drajnauth/TransistorTracer/Simulations/Testing Stuff/LM358 Amp.asc

R1: res; 10K
R4: res; 6K
R5: res; 1K
U1: opamp2; LM358
uC_Vcontrol: voltage; PULSE(0 4.6 0 4m 4m 0 8m 2)
Vcc: voltage; 14
Named nets: 0, Vout
.tran 20m
.lib TIP120.lib
.lib LM358.sub
.option fastaccess
