drajnauth/TransistorTracer/Simulations/Testing Stuff/PNP & NPN Voltage Amplifier.asc

Q1: npn; 2N3904
Q2: pnp; 2N3906
R1: res; 100K
R2: res; 100R
R3: res; 800K
V1: voltage; 14V
V2: voltage; PULSE(0 2.5 0 4m 4m 0 8m 2)
Named nets: 0, Vout, Vin
.tran 20m
