drajnauth/TransistorTracer/Simulations/Testing Stuff/2N3904 DC Amplifier  (10mA).asc

Q1: npn; 2N3904
Q2: npn; 2N3904
Q3: npn; 2SC5706
R1: res; 1500
R2: res; 10
R3: res; 56K
R4: res; 1500
R5: res; 10
R6: res; 240K
R7: res; 0.1
R8: res; 200
RL: res; 10R
V1: voltage; PULSE(0 4.8 0 5m 5m 0 10m 2)
V2: voltage; 14
Named nets: 0, Vc, Ve, Vb, Vin, Vc2, Ve2, Vb2, Vc3, Ve3, Vb3
.tran 12m
Original - Range of about 3.5V:
R3: 20K
R1, R4: 238R
R2, R5: 2R
R6: 56K
R8: 22 (for 200mA)
 
1st Mod - Wider Range > 4V:
R3: 20K
R1: 200R
R4: 238R
R2: 0R
R5: 1R
R6: 56K
R8: 22 (for 200mA)
 
14V Vcc - Range of about 3.5V:
R3: 20K
R1: 250R
R4: 238R
R2: 0R
R5: 0R
R6: 56K
R8: 22 (for 200mA)
