drajnauth/TransistorTracer/Simulations/Testing Stuff/2N3904 DC Amplifier - Collector Driver (10mA with Neg Feedback).asc

C1: cap; 1n
C2: cap; 14p
C3: cap; 1n
C4: cap; 14p
C5: polcap; 10µ; V=50 Irms=25m Rser=6.7 Lser=0
C6: cap; 10µ
Q1: npn; 2N3904
Q2: npn; 2N3904
Q3: npn; 2SC5706
Q5: npn; 2N3055
R1: res; 1500
R2: res; 10
R3: res; 56K
R4: res; 1500
R5: res; 10
R6: res; 240K
R7: res; 0.1
R8: res; 200
R9: res; 500
R10: res; {R}
R11: res; 462
R12: res; 10
R13: res; 66K
R14: res; 66K
R15: res; 34K
R16: res; 34K
V1: voltage; PULSE(0 4.8 0 5m 5m 0 10m 2)
V2: voltage; 14
V3: voltage; 13
V4: voltage; PULSE(0 4.7 0 1n 1n {DT}  256u); AC 1
V5: voltage; PULSE(0 4.7 128u 1n 1n {DT} 256u); AC 1
Named nets: 0, Vc, Ve, Vb, Vin, Vc2, Ve2, Vb2, Ve3, Vb3, Vadc1, Vadc2, Vpwm
.tran 100m
;.step param R 100 1000 100
.param R 1000
.step param DT 60u 160u 20u
