drajnauth/TransistorTracer/Simulations/Testing Stuff/Arduino PWM Test.asc

C1: polcap; 10µ; V=50 Irms=25m Rser=6.7 Lser=0
C2: polcap; 22µ; V=16 Irms=35m Rser=2.8 Lser=0
C3: polcap; 33µ; V=16 Irms=35m Rser=2.8 Lser=0
R1: res; 56K
R2: res; 200
R3: res; 4
V2: voltage; PULSE(0 4.8 0 1n 1n 128u 256u); AC 1
Named nets: 0, Vout
.tran 0 100m 45m
.step param R 10 200 10
