drajnauth/TransistorTracer/Simulations/Testing Stuff/LM386 Amp.asc

C1: polcap; 47µ; V=16 Irms=186m Rser=0.893291 Lser=4.92432n mfg="Würth Elektronik" pn="860160372007 WCAP-ATLL 5x11" type="Al electrolytic"
C10: polcap; 470µ; V=16 Irms=70m Rser=2.3 Lser=0
C11: polcap; 470µ; V=16 Irms=900m Rser=0.1 Lser=0 mfg="Nichicon" pn="UPH1C471MRH" type="Al electrolytic"
D1: schottky; 1N5817
D2: schottky; 1N5817
R8: res; 250
U1: LM386
V1: voltage; 12
V2: voltage; PULSE(0 2 0 1p 1p 16u 32u); AC 1
Named nets: 0, Vop, Vout
7 BP
1 G1
8 G8
.ac dec 100 1 100Meg
.inc LM386.sub
.tran 0 20m 19m
Convergence is too slow.  Is sufficient current output
Sweep duty cycle.  RMS voltage does not change as expected
