drajnauth/TransistorTracer/Simulations/Testing Stuff/PWM 2N3904 Amplifier.asc

Q1: npn; 2N3904
Q2: npn; 2N3904
R1: res; 1K
R3: res; 120K
R4: res; 100
R6: res; 3R
R7: res; 11K
V1: voltage; PULSE(0 4.8 0 5m 5m 100u 10.1m 2)
V2: voltage; 12
Named nets: 0, Vc, Ve, Vb, Vc2, Ve2, Vb2, Vin
.tran 12m
