drajnauth/TransistorTracer/Simulations/Testing Stuff/Current Ramp.asc

Q1: npn; 2N3904
Q2: npn; 2N3904
Q3: npn; 2N3055
R1: res; 100
R2: res; 10K
R3: res; 10K
R4: res; 10K
V1: voltage; 12
V2: voltage; PULSE(0 4.6 0 500u 500u 10u 1010u 1)
Named nets: 0, Vout
.tran 2m
