drajnauth/TransistorTracer/Simulations/Testing Stuff/Current Switch Test.asc

M1: nmos; 2N7000
R1: res; 100R
R2: res; 15K
R3: res; 500K
V1: voltage; 13.8V
V2: voltage; PULSE(0 5 0 1m 1m 10m 20m 1); AC 1
Named nets: 0
