drajnauth/TransistorTracer/Simulations/Testing Stuff/LM1013 Current Source Test.asc

Q1: npn; 2N2222A
R1: res; 100R
R2: res; 1K
R3: res; 10k
R4: res; 200R
R5: res; 7.14K
U1: LT1013
V1: voltage; 13.8V
V2: voltage; PULSE(0 5 0 5m 5m 15m 30m 1); AC 1
Named nets: 0, Vs
.tran 50m
