drajnauth/TransistorTracer/Simulations/Testing Stuff/LM1013 Peak Detector with Gain Test.asc

C1: polcap; 10µ; V=100 Irms=385m Rser=0.18 Lser=0
C2: polcap; 10µ; V=100 Irms=385m Rser=0.18 Lser=0
C3: polcap; 4.7µ; V=100 Irms=385m Rser=0.18 Lser=0
D1: schottky; 1N5711
D2: schottky; 1N5711
R1: res; 68K
R2: res; 1K
R3: res; 10k
R5: res; 7.14K
U1: LT1013
V1: voltage; 13.8V
V2: voltage; PULSE(0 5 0 1p 1p .5m 1m); AC 1
Named nets: 0, Vout
.tran 0 50m 30m
About 4ms Ripple
Delay 30m get about 16mV variation from 100ms.
