drajnauth/TransistorTracer/Simulations/Testing Stuff/NE5532 Amplifier.asc

C1: cap; 1µ
C2: cap; 1µ
C3: cap; 1µ
R1: res; 10K
R2: res; 1K
R3: res; 47K
R4: res; 47K
R5: res; 1K
U1: opamp2; NE5532
V2: voltage; 12
V5: voltage; SINE(0 .2 1500)
Named nets: 0, Vout
.inc NE5532.lib
.tran 10m
