drajnauth/TransistorTracer/Simulations/Testing Stuff/NE5532 Voltage Amplifier.asc

R1: res; 10K
R2: res; 1K
U1: opamp2; NE5532
V2: voltage; 13.8
V5: voltage; 5
Named nets: 0, Vout
.inc NE5532.sub
.tran 0 10m 9m
