drajnauth/TransistorTracer/Simulations/Testing Stuff/NMOS Characteristic Curve.asc

M1: nmos; IRF510
Rc: res; 10
Vb: voltage; 4.6
Vcc: voltage; 12
Named nets: 0, Vce
;.dc Vcc 0 40 .2 Vb 1 6 .25
.dc Vcc 0 40 .2
https://www.youtube.com/watch?v=7WWJ2kfJ3oc
