drajnauth/TransistorTracer/Simulations/Testing Stuff/NPN Basic Configuration.asc

Q2: npn; 2N3904
R5: res; 10K
R6: res; 1K
V2: voltage; PULSE(0 12 0 4m 1p 0 4p 2)
V3: voltage; PULSE(.8 1.2 4m 1p 1p 4m 4m 1)
Named nets: 0, Vout, Vc
.tran 8m
