drajnauth/TransistorTracer/Simulations/Testing Stuff/NPN Characteristic Load Line Curve.asc

Q1: npn; 2N3904
Rc: res; 10
Vb: voltage; 0
Vcc: voltage; 0
Named nets: 0, Vce
.dc Vb 0.1 1 .01
https://www.youtube.com/watch?v=7WWJ2kfJ3oc
