drajnauth/TransistorTracer/Simulations/Testing Stuff/NPN Configuration.asc

Q1: npn; 2N3904
R1: res; 9K
R2: res; 10K
R3: res; 9K
R4: res; 10K
Rb: res; 15K
Rc: res; 10K
U1: opamp2; lm358
U2: opamp2; lm358
V1: voltage; PULSE(0 5 0 10m 0 0 10m 2)
V2: voltage; PULSE(0.46 1 10m 1p 0 10m 10m 0)
V4: voltage; 12
Named nets: 0, Cve, Vb, +12, Vc_dac, Vb_dac, Vc, Vbin
.tran 20m
.inc LM358.sub
Not R2R Opamp
Gain: 1+10K/9K=2.1
Not R2R Opamp
Gain: 1+10K/9K=2.1
