drajnauth/TransistorTracer/Simulations/Testing Stuff/NPN FET Configuration 2.asc

M1: nmos; 2N7000
Q1: npn; 2N2222A
Q2: npn; 2N3904
R1: res; 38K
R2: res; 500
R3: res; 15K
R4: res; 10K
Rc1: res; 1K
V1: voltage; PULSE(5 0 100u 10m 0 0 10m 1)
V2: voltage; 3
V4: voltage; 12
Named nets: 0, Vc_max, Vc_control, Vout, Vb_control
.tran 10m
