drajnauth/TransistorTracer/Simulations/Testing Stuff/NPN FET Configuration.asc

M1: nmos; 2N7000
Q1: npn; 2N3904
R2: res; 700R
R3: res; 10K
Rb: res; 15K
V2: voltage; PULSE(2.1 1.6 0 4m 1p 0 4m 2)
V3: voltage; 12
V4: voltage; 12
V6: voltage; PULSE(.8 1 4m 1p 10 4m 1 1)
Named nets: 0, Vc, Vb, Vc_max, Vc_control, Vb_control, Vbin, Vb_max, Vc_source
.tran 8m
10K will limit current through transistor
What is the current limit for a transistor tracer.
