drajnauth/TransistorTracer/Simulations/Testing Stuff/NPN FET Test Configuration.asc

M1: nmos; IRF510
Q1: npn; 2N3904
Rb1: res; 1K
Rb: res; 15K
Rc: res; 10R
V2: voltage; PULSE(3.5 6 0 4m 1p 0 4m 2)
V3: voltage; 12
V4: voltage; 12
V6: voltage; PULSE(0.8 1.3 4m 1p 1p 4m 4m 1)
Named nets: 0, Vc, Vb, Vc_max, Vc_control, Vb_control, Vbin, Vb_max, Ve
.tran 8m
.include IRL510.sub
