drajnauth/TransistorTracer/Simulations/Testing Stuff/NPN Opamp Configuration.asc

Q1: npn; TIP41C
Q2: npn; 2N3904
R1: res; 10K
R2: res; 5K
R3: res; 1
R4: res; 10K
R5: res; 10K
R6: res; 100
U1: LT1013
V1: voltage; PULSE(0 4.6 0 4m 1p 0 4m 2)
V2: voltage; 12
V3: voltage; PULSE(.7 2 4m 1p 1p 4m 4m 1)
Named nets: 0, VcControl, Vout, Vc
.tran 8m
