drajnauth/TransistorTracer/Simulations/Testing Stuff/PNP Configuration - Input Trace.asc

Q1: npn; 2N3053
Q2: pnp; 2N3906
Q3: npn; 2N3904
Rb: res; 1K
Rc1: res; 15K
Rc2: res; 15K
Rc: res; 1
V1: voltage; 12
Vb: voltage; 0
Vcc: voltage; 0
Named nets: 0, Ve, Vc, Vb, Vcontrol
;tran 8m
Max ssems to be 1.4V
Ramp voltage and check current and Vce
Max seems to be 8V
Ramp voltage and check current and Vce
Will control transistors be fixed or dynamic control voltages
.dc Vb 0 2 .005
