drajnauth/TransistorTracer/Simulations/Testing Stuff/PNP Configuration - test.asc

Q2: pnp; 2N3906
Q3: npn; 2N3904
R1: res; 1K
Rb1: res; 15K
Rb: res; 1K
Rc: res; 10
V1: voltage; -0.8
Vb: voltage; 0
Vcc: voltage; 12
Named nets: Ve, Vc, Vbt, 0, Vcontrol
;tran 8m
Max ssems to be 1.4V
Ramp voltage and check current and Vce
Max seems to be 8V
Ramp voltage and check current and Vce
Will control transistors be fixed or dynamic control voltages
.dc Vb 0 4.6 0.05
