drajnauth/TransistorTracer/Simulations/Testing Stuff/PNP Model.asc

Q1: pnp; 2N3906
R1: res; 100R
R2: res; 50R
V1: voltage; 12
V2: voltage; PULSE(0 10 5m 100m .5m .5m 101m); AC 1
V3: voltage; PULSE(0 12 5m 1s 1m 1m 305m 1)
Named nets: 0, Vb, Vc, Vc1, Vc2
.tran 1s
