drajnauth/TransistorTracer/Simulations/Testing Stuff/PWM RC filter.asc

C1: cap; 33µ
R1: res; 1K
Rc1: res; 200
V1: voltage; PULSE(0 5 0 1p 1p 512u 1024u); AC 1
Named nets: 0
.tran 500m
