drajnauth/TransistorTracer/Simulations/Testing Stuff/TIP122-demo.asc

Q1: npn; TIP122
Rbase: res; 1k
Rload: res; 10R
V1: voltage; 5V
Named nets: 0
.lib TIP122.onsemi.lib
.tran 0 0.001 0 0.000001
