drajnauth/TransistorTracer/Simulations/Working/2N3904 DC Amplifier - Base Driver.asc

C1: cap; 1n
C2: cap; 14p
C3: cap; 1n
C4: cap; 14p
C5: polcap; 33µ; V=50 Irms=25m Rser=6.7 Lser=0
Q1: npn; 2N3904
Q2: npn; 2N3904
Q3: npn; 2SC5706
Q4: npn; 2N3904
Q5: npn; 2N3055
R1: res; 249
R2: res; .1
R3: res; 20K
R4: res; 237
R5: res; .1
R6: res; 56K
R7: res; 0.1
R8: res; 200
R9: res; 0.1
R10: res; 200
R11: res; 462
R12: res; 10R
R13: res; 66K
R14: res; 66K
R15: res; 34K
R16: res; 34K
R17: res; 220
RL: res; 10R
V1: voltage; PULSE(0 4.8 0 5m 5m 0 10m 2)
V2: voltage; 14
V3: voltage; PULSE(0 4.8 0 1n 1n 31u 32u); AC 1
Named nets: 0, Vc, Ve, Vb, Vin, Vc2, Ve2, Vb2, Ve3, Vb3, Vc4, Ve4, Vadc1, Vadc2, Vpwm
.tran 50m
Original - Range of about 3.5V:
R3: 20K
R1, R4: 238R
R2, R5: 2R
R6: 56K
R8: 22 (for 200mA)
 
1st Mod - Wider Range > 4V:
R3: 20K
R1: 200R
R4: 238R
R2: 0R
R5: 1R
R6: 56K
R8: 22 (for 200mA)
 
14V Vcc - Range of about 3.5V:
R3: 20K
R1: 250R
R4: 238R
R2: 0R
R5: 0R
R6: 56K
R8: 22 (for 200mA)
