drajnauth/TransistorTracer/Simulations/Working/Arduino PWM Analysis.asc

C1: polcap; 33µ; V=50 Irms=25m Rser=6.7 Lser=0
C2: cap; 1n
C3: cap; 14p
C4: cap; 1n
C5: cap; 14p
Q1: npn; 2N2222A
R1: res; 500
R2: res; 220
R3: res; 10R
R4: res; 66K
R5: res; 66K
R6: res; 34K
R7: res; 34K
V1: voltage; 12
V2: voltage; PULSE(0 4.8 0 1n 1n 31u 32u); AC 1
Named nets: 0, Vadc1, Vadc2, Vpwm, Vb
.tran 50m
