drajnauth/TransistorTracer/Simulations/Working/LM358 Opamp Voltage Source.asc

Q1: npn; 2N3055
R1: res; 10K
R2: res; 5K
R3: res; 1
R4: res; 10K
R5: res; 10R
U1: LT1013
V1: voltage; PULSE(0 4.6 100u 4m 1p 0 4m 1)
V2: voltage; 12
Named nets: 0, Vb, Vout
.tran 5m
