drajnauth/TransistorTracer/Simulations/Working/Voltage Multiplier with LM358.asc

C1: cap; 47µ
C2: cap; 100µ
D1: schottky; 1N5711
D2: schottky; 1N5711
Q3: npn; TIP120
R1: res; 10K
R3: res; 10R
R4: res; 1K
R5: res; 1K
U1: opamp2; LM358
uC_Pulse: voltage; PULSE(0 4.8 0 1n 1n 50u 100u)
uC_Vcontrol: voltage; PULSE(0 4.6 11m 4m 1p 0 4m 2)
Vcc: voltage; 12
Named nets: 0, Vout
.tran 0 20m 10u 500u startup uic
.lib TIP120.lib
.lib LM358.sub
.option fastaccess
