drajnauth/TransistorTracer/Software/Nano NPN-NMOS Transistor Tracer v0.2b/trace.cpp

#include "trace.h"

#include <Arduino.h>

#include "defines.h"
#include "main.h"
#include "nfet.h"
#include "npn.h"
#include "trace.h"

extern struct TRACE_TRANS_STRUT *pts;
extern struct TRACE_FET_STRUT *pfs;

extern unsigned long flags;

float ib_u, ic_u, vbe_u, vbc_u, id_u, vce_u, vgs_u, vds_u;

void displayVoltages(void) {
  ib_u = pts->ib;
  ic_u = pts->ic;
  id_u = pfs->id;
  vbe_u = pts->vbe;
  vce_u = pts->vce;
  vgs_u = pfs->vgs;
  vds_u = pfs->vds;
  vbc_u = pts->vbc;
  if (pfs->units == 'M' || pfs->units == 'M') {
    ib_u *= 1000.0;
    ic_u *= 1000.0;
    id_u *= 1000.0;
    vbe_u *= 1000.0;
    vce_u *= 1000.0;
    vbc_u *= 1000.0;
    vgs_u *= 1000.0;
    vds_u *= 1000.0;
  } else if (pfs->units == 'U' || pfs->units == 'U') {
    ib_u *= 1000000.0;
    ic_u *= 1000000.0;
    id_u *= 1000000.0;
    vbe_u *= 1000000.0;
    vce_u *= 1000000.0;
    vbc_u *= 1000000.0;
    vgs_u *= 1000000.0;
    vds_u *= 1000000.0;
  }

  //////////////////////////////////
  ////// SWEEP_BJT_OUTPUT_DATA
  //////////////////////////////////
  if (flags & SWEEP_BJT_OUTPUT_DATA) {
    if (flags & EXPORT_DATA) {
      if (!pts->header) {
        Serial.println("#Ib,Vce,Ic");
        pts->header = 0xff;
      }
      Serial.print("#");
    }

    Serial.print(pts->ib, 12);
    Serial.print(",");
    Serial.print(pts->vce, 12);
    Serial.print(",");
    Serial.println(ic_u, 12);

    //////////////////////////////////
    ////// SWEEP_DIODE_INPUT_DATA
    //////////////////////////////////
  } else if (flags & SWEEP_DIODE_INPUT_DATA) {
    if (flags & EXPORT_DATA) {
      if (!pts->header) {
        Serial.println("#V,I");
        pts->header = 0xff;
      }
      Serial.print("#");
    }
    Serial.print(vbe_u, 20);
    Serial.print(",");
    Serial.println(ib_u, 12);

    //////////////////////////////////
    ////// SWEEP_DIODE_OUTPUT_DATA
    //////////////////////////////////
  } else if (flags & SWEEP_DIODE_OUTPUT_DATA) {
    if (flags & EXPORT_DATA) {
      if (!pts->header) {
        Serial.println("#If,Vf");
        pts->header = 0xff;
      }
      Serial.print("#");
    }
    Serial.print(
        pts->ic,
        20);  // this contains an integer couter to flatten out the curve
    Serial.print(",");
    Serial.println(vbc_u, 12);

    //////////////////////////////////
    ////// SWEEP_BJT_INPUT_DATA
    //////////////////////////////////
  } else if (flags & SWEEP_BJT_INPUT_DATA ||
             flags & SWEEP_BJT_INPUT_DATA_BY_VCE) {
    if (flags & EXPORT_DATA) {
      if (!pts->header) {
        if (flags & SWEEP_BJT_INPUT_DATA) {
          Serial.println("#Vbe,Ic");
        } else {
          Serial.println("#Vbe,Vce");
        }
        pts->header = 0xff;
      }
      Serial.print("#");
    }
    if (flags & SWEEP_BJT_INPUT_DATA) {
      Serial.print(vbe_u, 20);
      Serial.print(",");
      Serial.println(ic_u, 12);
    } else {
      Serial.print(vbe_u, 20);
      Serial.print(",");
      Serial.println(vce_u, 12);
    }

    //////////////////////////////////
    ////// SWEEP_BJT_BETA_DATA
    ////// SWEEP_BJT_BETAC_DATA
    //////////////////////////////////
  } else if (flags & SWEEP_BJT_BETA_DATA || flags & SWEEP_BJT_BETAC_DATA) {
    if (pts->ib == 0) {
      Serial.println("ER");
      return;
    }
    if (flags & EXPORT_DATA) {
      if (!pts->header) {
        if (flags & SWEEP_BJT_BETAC_DATA) {
          Serial.println("#Ic,beta");
        } else {
          Serial.println("#Ib,beta");
        }
        pts->header = 0xff;
      }
      Serial.print("#");
    }

    if (flags & SWEEP_BJT_BETAC_DATA) {
      Serial.print(ic_u, 12);
    } else {
      Serial.print(ib_u, 12);
    }
    Serial.print(",");
    Serial.println(pts->beta, 8);

    //////////////////////////////////
    ////// SWEEP_BJT_RE_DATA
    //////////////////////////////////
  } else if (flags & SWEEP_BJT_RE_DATA) {
    if (flags & EXPORT_DATA) {
      if (!pts->header) {
        Serial.println("#Vbe,Re");
        pts->header = 0xff;
      }
      Serial.print("#");
    }

    Serial.print(pts->vbe, 20);
    Serial.print(",");
    Serial.println(pts->re, 12);

    //////////////////////////////////
    ////// SWEEP_BJT_GM_DATA
    //////////////////////////////////
  } else if (flags & SWEEP_BJT_GM_DATA) {
    if (flags & EXPORT_DATA) {
      if (!pts->header) {
        Serial.println("#Vbe,gm");
        pts->header = 0xff;
      }
      Serial.print("#");
    }
    pts->gm = pts->ic / THERMAL_VOLTAGE;
    Serial.print(pts->vbe, 20);
    Serial.print(",");
    Serial.println(pts->gm, 12);

    //////////////////////////////////
    ////// SWEEP_FET_INPUT_DATA
    //////////////////////////////////
  } else if (flags & SWEEP_FET_INPUT_DATA ||
             flags & SWEEP_FET_VOLTAGE_INPUT_DATA) {
    if (flags & EXPORT_DATA) {
      if (!pts->header) {
        if (flags & SWEEP_FET_INPUT_DATA) {
          Serial.println("#Vgs,Id");
        } else {
          Serial.println("#Vgs,Vds");
        }

        pts->header = 0xff;
      }
      Serial.print("#");
    }

    if (flags & SWEEP_FET_INPUT_DATA) {
      Serial.print(pfs->vgs, 20);
      Serial.print(",");
      Serial.println(id_u, 12);
    } else {
      Serial.print(pfs->vgs, 20);
      Serial.print(",");
      Serial.println(vds_u, 12);
    }

    //////////////////////////////////
    ////// SWEEP_FET_OUTPUT_DATA
    //////////////////////////////////
  } else if (flags & SWEEP_FET_OUTPUT_DATA) {
    if (flags & EXPORT_DATA) {
      if (!pts->header) {
        Serial.println("#Vgs,Vds,Id");
        pts->header = 0xff;
      }
      Serial.print("#");
    }
    Serial.print(pfs->vgs, 12);
    Serial.print(",");
    Serial.print(pfs->vds, 12);
    Serial.print(",");
    Serial.println(id_u, 12);

    //////////////////////////////////
    ////// SWEEP_FET_K_DATA
    //////////////////////////////////
  } else if (flags & SWEEP_FET_K_DATA) {
    if (flags & EXPORT_DATA) {
      if (!pts->header) {
        Serial.println("#Id,k");
        pts->header = 0xff;
      }
      Serial.print("#");
    }
    Serial.print(pfs->id, 12);
    Serial.print(",");
    Serial.println(pts->k, 12);

    //////////////////////////////////
    ////// SWEEP_FET_GM_DATA
    //////////////////////////////////
  } else if (flags & SWEEP_FET_GM_DATA) {
    if (flags & EXPORT_DATA) {
      if (!pts->header) {
        Serial.println("#Id,gm");
        pts->header = 0xff;
      }
      Serial.print("#");
    }
    Serial.print(pfs->id, 12);
    Serial.print(",");
    Serial.println(pts->gm, 12);

    //////////////////////////////////
    ////// SWEEP_FET_R_DATA
    //////////////////////////////////
  } else if (flags & SWEEP_FET_R_DATA) {
    if (flags & EXPORT_DATA) {
      if (!pts->header) {
        Serial.println("#Id,Rds");
        pts->header = 0xff;
      }
      Serial.print("#");
    }

    Serial.print(pfs->id, 12);
    Serial.print(",");
    Serial.println(pfs->rds, 12);

  } else {
    Serial.print(" VccVoltage: ");
    Serial.print(pts->VccVoltage, 4);
    Serial.print(" VcVoltage: ");
    Serial.print(pts->VcVoltage, 4);
    Serial.print(" DeltaV: ");
    Serial.print(pts->vcr, 4);
    Serial.print(" Ic: ");
    Serial.println(pts->ic, 6);

    Serial.print(" Vb1 Voltage: ");
    Serial.print(pts->Vb1Voltage, 4);
    Serial.print(" Vb2 Voltage: ");
    Serial.println(pts->Vb2Voltage, 4);
    Serial.print(" DeltaV: ");
    Serial.print(pts->vbr, 4);
    Serial.print(" Ib: ");
    Serial.println(pts->ib, 6);
    Serial.print("Vbe: ");
    Serial.print(pts->vbe, 4);
    Serial.print(" Beta: ");
    Serial.println(pts->beta, 2);
  }
}

void getMinMaxVoltages(void) {
  float maxvol = 0;
  float maxcon = 0;
  float minvol = 0;
  float mincon = 0;
  float lastvol = 0;
  float diff = 0;
  unsigned char ctr = 0;
  int pwm = 0;
  int i = 0;
  unsigned char loop = 0;
  unsigned char print = 0;
  float sumx = 0;
  float sumy = 0;
  float sumx2 = 0;
  float sumxy = 0;

  pts->bSlope = pts->bInt = pts->cSlope = pts->cInt = 0;

  Serial.println("Vb cal");
  for (pwm = 0; pwm < 256; pwm++) {
    analogWrite(pts->VbOutPin, pwm);
    delay(PWM_SETTLE_TIME);
    measureVoltages();
    analogWrite(pts->VbOutPin, 0);  // Reduce heating
    diff = (pts->Vb1Voltage - lastvol);

    pts->VbControl = map(pwm, 0, 255, 0, MAX_SCALED_VOLTAGE);
    pts->VbControl /= (float)VOLTAGE_SCALING;

    if (minvol == 0 && pts->Vb1Voltage > VOLTAGE_ON_THRESHOLD) {
      minvol = pts->Vb1Voltage;
      mincon = pts->VbControl;
    }

    if (maxvol < pts->Vb1Voltage) {
      if (diff > 0 && diff > 0.001) {
        maxvol = pts->Vb1Voltage;
        maxcon = pts->VbControl;

        ctr = 0;
        if (minvol > 0) {
          i++;
          sumx += pts->VbControl;
          sumy += pts->Vb1Voltage;
          sumx2 += (pts->VbControl * pts->VbControl);
          sumxy += (pts->VbControl * pts->Vb1Voltage);
        }
      }
    } else if (pts->Vb1Voltage > 0 && (diff < 0 || diff < 0.00001)) {
      if (ctr++ > 10) {
        pwm = 300;
      }
    }

    if (++loop >= print) {
      Serial.print(loop);
      Serial.println("/255");
      print += 15;
    }

    lastvol = pts->Vb1Voltage;
  }
  if (i > 0) {
    pts->VbControlMin = mincon;
    pts->VbControlMax = maxcon;
    pts->VbControlInc =
        (pts->VbControlMax - pts->VbControlMin) / (float)pts->nvb;
    if (pts->VbControlInc < PWM_RESOLUTION) pts->VbControlInc = PWM_RESOLUTION;
    pts->vbmin = minvol;
    pts->vbmax = maxvol;
    pts->vbinc = (pts->vbmax - pts->vbmin) / (float)pts->nvb;

    lastvol = i * sumx2 - sumx * sumx;
    if (lastvol != 0) {
      pts->bSlope = (i * sumxy - sumx * sumy) / lastvol;
      pts->bInt = (sumx2 * sumy - sumx * sumxy) / lastvol;
    } else {
      pts->bSlope = 0;
      pts->bInt = 0;
    }

    Serial.print("Max Vb: ");
    Serial.print(maxvol);
    Serial.print(" at con: ");
    Serial.print(maxcon);
    Serial.print(" VbCalM: ");
    Serial.print(pts->bSlope, 3);
    Serial.print(" VbCalB: ");
    Serial.println(pts->bInt, 3);
    printOutputVoltageValues(BASE_VALUES);
    printControlValues(BASE_VALUES);

  } else {
    Serial.println("Vb Err");
  }

  sumx = 0;
  sumy = 0;
  sumx2 = 0;
  sumxy = 0;

  maxvol = 0;
  maxcon = 0;
  minvol = 0;
  mincon = 0;
  lastvol = 0;
  diff = 0;
  ctr = 0;
  i = 0;
  loop = 0;
  print = 0;
  Serial.println("Vc cal");
  for (pwm = 0; pwm < 256; pwm++) {
    analogWrite(pts->VccOutPin, pwm);
    delay(PWM_SETTLE_TIME);
    measureVoltages();
    analogWrite(pts->VccOutPin, 0);  // Reduce heating

    diff = (pts->VccVoltage - lastvol);

    pts->VcControl = map(pwm, 0, 255, 0, MAX_SCALED_VOLTAGE);
    pts->VcControl /= (float)VOLTAGE_SCALING;

    if (minvol == 0 && pts->VccVoltage > VOLTAGE_ON_THRESHOLD) {
      minvol = pts->VccVoltage;
      mincon = pts->VcControl;
    }

    if (maxvol < pts->VccVoltage) {
      if (diff > 0 && diff > 0.001) {
        maxvol = pts->VccVoltage;
        maxcon = pts->VcControl;

        ctr = 0;

        if (minvol > 0) {
          i++;
          sumx += pts->VcControl;
          sumy += pts->VccVoltage;
          sumx2 += (pts->VcControl * pts->VcControl);
          sumxy += (pts->VcControl * pts->VccVoltage);
        }
      }

    } else if (pts->Vb1Voltage > 0 && (diff < 0 || diff < 0.00001)) {
      if (ctr++ > 10) {
        pwm = 300;
      }
    }

    if (++loop >= print) {
      Serial.print(loop);
      Serial.println("/255");
      print += 15;
    }

    lastvol = pts->VccVoltage;
  }
  if (i > 0) {
    pts->VcControlMin = mincon;
    pts->VcControlMax = maxcon;
    pts->VcControlInc =
        (pts->VcControlMax - pts->VcControlMin) / (float)pts->nvc;
    if (pts->VcControlInc < PWM_RESOLUTION) pts->VcControlInc = PWM_RESOLUTION;
    pts->vcmin = minvol;
    pts->vcmax = maxvol;
    pts->vcinc = (pts->vcmax - pts->vcmin) / (float)pts->nvc;
    if (pts->vcinc < PWM_RESOLUTION) pts->vcinc = PWM_RESOLUTION;

    lastvol = i * sumx2 - sumx * sumx;
    if (lastvol != 0) {
      pts->cSlope = (i * sumxy - sumx * sumy) / lastvol;
      pts->cInt = (sumx2 * sumy - sumx * sumxy) / lastvol;
    } else {
      pts->cSlope = 0;
      pts->cInt = 0;
    }

    Serial.print("Max Vcc: ");
    Serial.print(maxvol);
    Serial.print(" at con: ");
    Serial.print(maxcon);
    Serial.print(" VcCalM: ");
    Serial.print(pts->cSlope, 3);
    Serial.print(" VcCalB: ");
    Serial.println(pts->cInt, 3);
    printOutputVoltageValues(COLLECTOR_VALUES);
    printControlValues(COLLECTOR_VALUES);
  } else {
    Serial.println("Vc Err");
  }

  resetPins();
  clearSweepFlags();
}

void setUpPWM(void) {
  // Pin 10 is OC1B attached to timer 1
  // Pin 9 is OC2B attached to timer 2
  // Normal timer operation is 900 Hz, need to run at 31KHz
  TCCR1B = ((TCCR1B) & (B11111000)) |
           (B00000001);  // Clear prescalers bits and then set precaler 1 for
                         // timer 1.  Neeed for PWM frequency of 31372.55 Hz
  TCCR2B = ((TCCR2B) & (B11111000)) |
           (B00000001);  // Clear prescalers bits and then set precaler 1 for
                         // timer 2.  Neeed for PWM frequency of 31372.55 Hz
}

int calculatePWM(float voltage) {
  int scaledVoltage = 0;  // voltage x1024 (i.e. shift 10 bits). Max voltage
                          // is 1024x5 = 5120 (i.e 5V)
  int outputValue = 0;    // value output to the PWM (analog out)

  scaledVoltage = int((float)(voltage * (float)VOLTAGE_SCALING));
  outputValue = map(scaledVoltage, 0, MAX_SCALED_VOLTAGE, 0, 255);
  return outputValue;
}

void setVoltage(int pin, float voltage) {
  analogWrite(pin, calculatePWM(voltage));
}

float convertOutputToControl(float vol, char type) {
  if (type == COLLECTOR_VALUES) {
    return ((vol - pts->cInt) / pts->cSlope);
  } else if (type == BASE_VALUES) {
    return ((vol - pts->bInt) / pts->bSlope);
  }
  return 0;
}

float convertControlToOutput(float vol, char type) {
  if (type == COLLECTOR_VALUES) {
    return ((vol * pts->cSlope + pts->cInt));
  } else if (type == BASE_VALUES) {
    return ((vol * pts->bSlope + pts->bInt));
  }
  return 0;
}

int adcAverage(int pin, unsigned char average) {
  unsigned char i;
  unsigned char iterations;
  unsigned long total;

  iterations = 1 << average;

  total = 0;
  for (i = 0; i < iterations; i++) {
    total += analogRead(pin);
  }
  total = total >> average;

  return (int)total;
}

void measureVoltages(void) {
  int temp;

  temp = adcAverage(pts->VccVoltagePin, ADC_BIT_SHIFT_AVERAGE);
  pts->VccVoltage = (float)temp / ADC_CONVERSION;

  temp = adcAverage(pts->VcVoltagePin, ADC_BIT_SHIFT_AVERAGE);
  pts->VcVoltage = (float)temp / ADC_CONVERSION;

  temp = adcAverage(pts->Vb1VoltagePin, ADC_BIT_SHIFT_AVERAGE);
  pts->Vb1Voltage = (float)temp / LOW_ADC_CONVERSION;

  temp = adcAverage(pts->Vb2VoltagePin, ADC_BIT_SHIFT_AVERAGE);
  pts->Vb2Voltage = (float)temp / LOW_ADC_CONVERSION;

  pts->vcr = pts->VccVoltage - pts->VcVoltage;
  pts->vbr = pts->Vb1Voltage - pts->Vb2Voltage;
  pts->vcc = pts->VccVoltage;
  pfs->vgd = pts->vbc = pts->VcVoltage - pts->Vb2Voltage;

  pfs->ig = pts->ib = pts->vbr / (float)pts->rbResistor;
  pfs->id = pts->ic = pts->vcr / (float)pts->rcResistor;
  if (pts->ib > 0) {
    pts->beta = pts->ic / pts->ib;
  } else {
    pts->beta = 0;
  }

  pts->vbe = pfs->vgs = pts->Vb2Voltage;
  pfs->vds = pts->vce = pts->VcVoltage;
  if (pfs->id != 0) {
    pts->re = pfs->rds = pfs->vds / pfs->id;
  } else {
    pts->re = pfs->rds = 0;
  }
}

float getVccVoltage(void) {
  float temp;
  temp = adcAverage(pts->PowerOnAnalogPin, ADC_BIT_SHIFT_AVERAGE);
  temp *= VOLTAGE_SENSE_CONVERSION;
  return temp;
}

float checkVcc(char type) {
  float vol = 0;

  if (type) {
    vol = getVccVoltage();
    if (vol <= MIN_ALLOWED_VCC_VOLTAGE || vol > MAX_ALLOWED_VCC_VOLTAGE) {
      return vol;
    }
  } else {
    if (!digitalRead(pts->PowerOnDigitalPin)) {
      return 1;
    }
  }
  return 0;
}

void waitForVcc(char type) {
  float vol = 0;

  if (type) {
    while ((vol = checkVcc(CHECK_ANALOG_VCC))) {
      Serial.print("Err. Vcc: ");
      Serial.println(vol, 1);
      digitalWrite(LED_BUILTIN, HIGH);
      delay(500);
      digitalWrite(LED_BUILTIN, LOW);
      delay(500);
    }
  } else {
    while (!digitalRead(pts->PowerOnDigitalPin)) {
      vol = getVccVoltage();
      Serial.print("Vcc Err.  Vcc: ");
      Serial.println(vol, 1);
      digitalWrite(LED_BUILTIN, HIGH);
      delay(500);
      digitalWrite(LED_BUILTIN, LOW);
      delay(500);
    }
  }
}

void resetPins() {
  pinMode(LED_BUILTIN, OUTPUT);
  digitalWrite(LED_BUILTIN, 0);  // Turn off LED

  pinMode(pts->VccVoltagePin, INPUT);  // ADC input port
  pinMode(pts->VcVoltagePin, INPUT);   // ADC input port
  pinMode(pts->Vb1VoltagePin, INPUT);  // ADC input port
  pinMode(pts->Vb2VoltagePin, INPUT);  // ADC input port
  pinMode(pts->PowerOnAnalogPin, INPUT);

  analogReference(DEFAULT);  // Use 5v reference

  pinMode(pts->VccOutPin, OUTPUT);
  pinMode(pts->VbOutPin, OUTPUT);
  pinMode(pts->PowerOnDigitalPin, INPUT);

  digitalWrite(pts->VccVoltagePin, 0);      // disable pullup
  digitalWrite(pts->VcVoltagePin, 0);       // disable pullup
  digitalWrite(pts->Vb1VoltagePin, 0);      // disable pullup
  digitalWrite(pts->Vb2VoltagePin, 0);      // disable pullup
  digitalWrite(pts->PowerOnDigitalPin, 0);  // disable pullup

  digitalWrite(pts->VccOutPin, 0);  // Zero output
  digitalWrite(pts->VbOutPin, 0);   // Zero output
  setUpPWM();

  setVoltage(pts->VccOutPin, 0);
  setVoltage(pts->VbOutPin, 0);

  delay(PWM_SETTLE_TIME);
}

void resetVoltages(void) {
  pts->VccVoltage = 0;
  pts->VcVoltage = 0;
  pts->Vb1Voltage = 0;
  pts->Vb2Voltage = 0;

  pts->VcControl = 0;
  pts->VbControl = 0;

  pts->vbr = pts->vcr = pts->vc = pts->ve = pts->vcc = 0;
  pts->ic = pts->ib = pts->vce = pts->vbe = pts->vbc = 0;
  pfs->id = pfs->ig = pfs->vgs = pfs->vds = pfs->vgd = pfs->rds;
  pfs->rds_th = pfs->ids_on = pfs->vgs_on = pfs->vgs_th = 0;
  pts->k = pts->gm = pts->beta = 0;
  ib_u = ic_u = vbe_u = vbc_u = id_u = vce_u = vgs_u = vds_u = 0;
}

void setDefaultLimits(void) {
  pts->version = EEPROM_HEADER;

  pts->VccVoltagePin = VCCADC;       // NPN Vcc measure voltage.
  pts->VcVoltagePin = VCADC;         // NPN Vc measure voltage.
  pts->Vb1VoltagePin = VB1ADC;       // NPN Vb1 measure voltage.
  pts->Vb2VoltagePin = VB2ADC;       // NPN Vb2 measure voltage.
  pts->VccOutPin = VCC_CONTROL_PIN;  // PWM NPN Vc controlOutput pin
  pts->VbOutPin = VB_CONTROL_PIN;    // PWM NPN Vb control Output pin
  pts->PowerOnDigitalPin =
      VCC_DIGITAL_PIN;  // Digital sense pin for Vcc is connected
  pts->PowerOnAnalogPin = VCC_ANALOG_PIN;  // Vcc voltage measurement

  pts->rcResistor = pts->rbResistor = 0;
  pts->bSlope = pts->bInt = pts->cSlope = pts->cInt = 0;

  pts->VcControlMin = MIN_VC_VOLTAGE;
  pts->VcControlMax = MAX_VC_VOLTAGE;
  pts->VcControlInc = (pfs->vdmax - pfs->vdmin) / (float)pfs->nvd;
  ;
  pts->VbControlMin = MIN_VB_VOLTAGE;
  pts->VbControlMax = MAX_VB_VOLTAGE;
  pts->VbControlInc = (pfs->vgmax - pfs->vgmin) / (float)pfs->nvg;

  pfs->units = 'D';
  pfs->nvd = NUM_VC_VOLTAGE;
  pfs->nvg = NUM_VB_VOLTAGE;
  pfs->vdmin = 0;
  pfs->vdmax = 0;
  pfs->vdinc = 0;

  pfs->vgmin = 0;
  pfs->vgmax = 0;
  pfs->vginc = 0;

  pfs->VgControl = 0;
  pfs->VdControl = 0;
}

void clearSweepFlags(void) {
  // BJT Flags
  flags &= ~SWEEP_BJT_OUTPUT_DATA;
  flags &= ~SWEEP_FET_OUTPUT_DATA;
  flags &= ~SWEEP_BJT_INPUT_DATA;
  flags &= ~SWEEP_BJT_BETA_DATA;
  flags &= ~SWEEP_BJT_INPUT_DATA_BY_VCE;
  flags &= ~SWEEP_BJT_BETAC_DATA;
  flags &= ~SWEEP_BJT_RE_DATA;
  flags &= ~SWEEP_BJT_GM_DATA;
  // FET Flags
  flags &= ~SWEEP_FET_VOLTAGE_INPUT_DATA;
  flags &= ~SWEEP_FET_K_DATA;
  flags &= ~SWEEP_FET_GM_DATA;
  flags &= ~SWEEP_FET_INPUT_DATA;
  flags &= ~SWEEP_FET_R_DATA;
  // Diode flags
  flags &= ~SWEEP_DIODE_INPUT_DATA;
  flags &= ~SWEEP_DIODE_OUTPUT_DATA;
  // Misc Flags
  flags &= ~PRINT_ADC_VALUES;
  flags &= ~EXPORT_DATA;
}

void printResistorValues(char type) {
  if (type == COLLECTOR_VALUES || type == ALL_VALUES) {
    Serial.print("Rc/Rd: ");
    Serial.println(pts->rcResistor);
  }
  if (type == BASE_VALUES || type == ALL_VALUES) {
    Serial.print("Rb/Rg: ");
    Serial.println(pts->rbResistor);
  }
}

unsigned char checkResistors(char type, char announce) {
  unsigned char bad = 0;
  if (type == COLLECTOR_VALUES || type == ALL_VALUES) {
    if ((pts->rcResistor == RC_RESISTORLOW ||
         pts->rcResistor == RC_RESISTORHIGH)) {
      if (announce) {
        printResistorValues(COLLECTOR_VALUES);
      }
      bad++;
    } else {
      if (announce) {
        Serial.println("Rc/Rd err");
      }
    }
  }
  if (type == BASE_VALUES || type == ALL_VALUES) {
    if (pts->rbResistor == RB_RESISTOR) {
      if (announce) {
        printResistorValues(BASE_VALUES);
      }
      bad++;
    } else {
      if (announce) {
        Serial.println("Rb/Rg err");
      }
    }
  }
  return bad;
}

unsigned char checkSweepRange(void) {
  unsigned char bad = 0;
  if (pfs->nvg > 0 && pfs->nvd > 0) {
    bad++;
  }
  if (pfs->vdinc > 0 && pfs->vginc > 0) {
    bad++;
  }
  if (pfs->vdmin >= pfs->vdmax && pfs->vdmax != 0 && pfs->vgmin <= pfs->vgmax &&
      pfs->vgmax != 0) {
    bad++;
  }
  return bad;
}

void printConfig(char type) {
  if (type == BASE_VALUES || type == ALL_VALUES) {
    printControlValues(BASE_VALUES);

    Serial.print("Max/Min Vb/Vg: ");
    Serial.print(pts->vbmin, 3);
    Serial.print(" - ");
    Serial.print(pts->vbmax, 3);
    Serial.print("  points: ");
    Serial.print(pts->nvb);
    Serial.print(" delta: ");
    Serial.println(pts->vbinc, 3);

    Serial.print("Rb/Rg: ");
    Serial.print(pts->rbResistor);
    Serial.print(" VbCalM: ");
    Serial.print(pts->bSlope, 3);
    Serial.print(" VbCalB: ");
    Serial.println(pts->bInt, 3);
  }

  if (type == COLLECTOR_VALUES || type == ALL_VALUES) {
    printControlValues(COLLECTOR_VALUES);

    Serial.print("Max/Min Vc/Vd: ");
    Serial.print(pts->vcmin, 3);
    Serial.print(" - ");
    Serial.print(pts->vcmax, 3);
    Serial.print(" points: ");
    Serial.print(pts->nvc);
    Serial.print(" delta: ");
    Serial.println(pts->vcinc, 3);

    Serial.print("Rc/Rd: ");
    Serial.print(pts->rcResistor);
    Serial.print(" VcCalM: ");
    Serial.print(pts->cSlope, 3);
    Serial.print(" VcCalB: ");
    Serial.println(pts->cInt, 3);
    ;
  }
}

void printControlValues(char type) {
  if (type == BASE_VALUES || type == ALL_VALUES) {
    Serial.print("Control Vb/Vg: ");
    Serial.print(pts->VbControlMin, 3);
    Serial.print(" - ");
    Serial.print(pts->VbControlMax, 3);
    Serial.print("  points: ");
    Serial.print(pts->nvb);
    Serial.print(" delta: ");
    Serial.println(pts->VbControlInc, 3);
  }

  if (type == COLLECTOR_VALUES || type == ALL_VALUES) {
    Serial.print("Control Vc/Vd: ");
    Serial.print(pts->VcControlMin, 3);
    Serial.print(" - ");
    Serial.print(pts->VcControlMax, 3);
    Serial.print(" points: ");
    Serial.print(pts->nvc);
    Serial.print(" delta: ");
    Serial.println(pts->VcControlInc, 3);
  }

  if (type == INPUT_SWEEP_VALUES) {
    Serial.print("Control Vb/Vg: ");
    Serial.print(pts->VbControlMin, 3);
    Serial.print(" - ");
    Serial.print(pts->VbControlMax, 3);
    Serial.print("  points: ");
    Serial.print(pts->nvb);
    Serial.print(" delta: ");
    Serial.println(pts->VbControlInc, 3);
    Serial.print("Fixed Vc/Vd: ");
    Serial.println(pts->VcControlMax, 3);
  }
}

void printOutputVoltageValues(char type) {
  if (type == BASE_VALUES || type == ALL_VALUES) {
    Serial.print("Output Vb/Vg: ");
    Serial.print(convertControlToOutput(pts->VbControlMin, BASE_VALUES), 3);
    Serial.print(" - ");
    Serial.print(convertControlToOutput(pts->VbControlMax, BASE_VALUES), 3);
    Serial.print("  points: ");
    Serial.print(pts->nvb);
    Serial.print(" delta: ");
    Serial.println(convertControlToOutput(pts->VbControlInc, BASE_VALUES), 3);
  }

  if (type == COLLECTOR_VALUES || type == ALL_VALUES) {
    Serial.print("Output Vc/Vd: ");
    Serial.print(convertControlToOutput(pts->VcControlMin, COLLECTOR_VALUES),
                 3);
    Serial.print(" - ");
    Serial.print(convertControlToOutput(pts->VcControlMax, COLLECTOR_VALUES),
                 3);
    Serial.print("  points: ");
    Serial.print(pts->nvc);
    Serial.print(" delta: ");
    Serial.println(convertControlToOutput(pts->VcControlInc, COLLECTOR_VALUES),
                   3);
  }

  if (type == INPUT_SWEEP_VALUES) {
    Serial.print("Output Vb/Vg: ");
    Serial.print(convertControlToOutput(pts->VbControlMin, BASE_VALUES), 3);
    Serial.print(" - ");
    Serial.print(convertControlToOutput(pts->VbControlMax, BASE_VALUES), 3);
    Serial.print("  points: ");
    Serial.print(pts->nvb);
    Serial.print(" delta: ");
    Serial.println(convertControlToOutput(pts->VbControlInc, BASE_VALUES), 3);
    Serial.print("Fixed Vc/Vd: ");
    Serial.println(convertControlToOutput(pts->VcControlMax, COLLECTOR_VALUES),
                   3);
  }
}
